Hasatio/esp32DevKitL/Rev2/3d/5040771891.stp

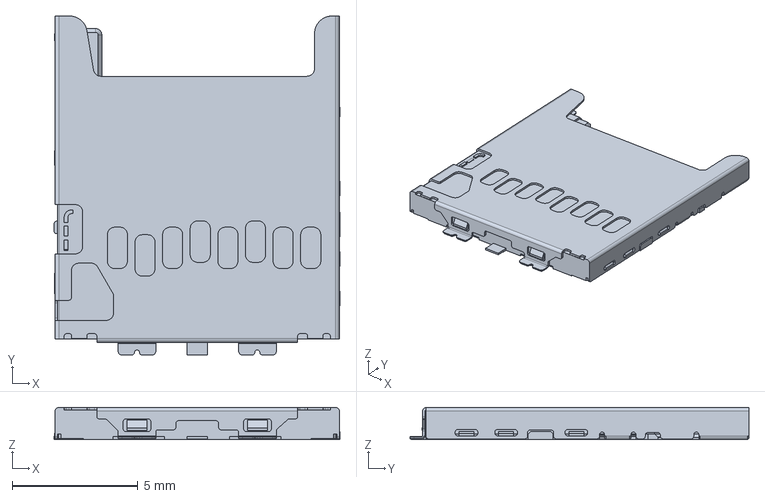
[picture p15: CAD file, 2023-03-13]
Rev2/3d/5040771891.stp
11.4 x 13.5 x 1.28 mm
